norayr-noro/Devboard-RGB-LED-custom_button_I2C_header/Photoss/PCB_screenshot(3d-front).png

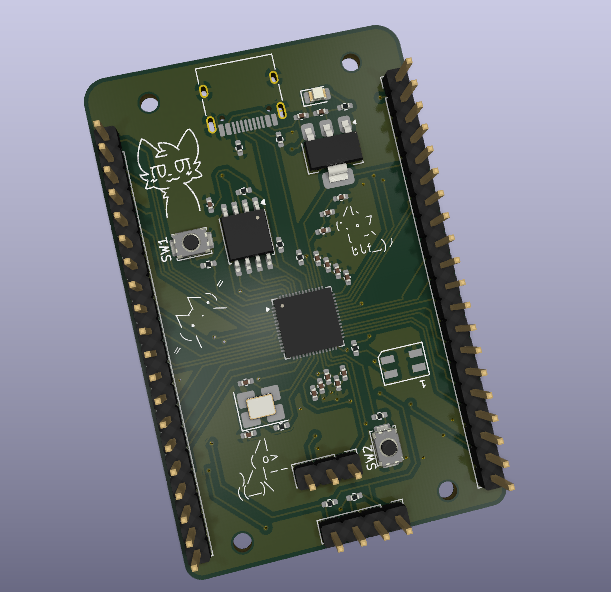
Photoss/PCB_screenshot(3d-front).png
