norayr-noro/Devboard-RGB-LED-custom_button_I2C_header/Photoss/Screenshot 2026-04-28 124610.png

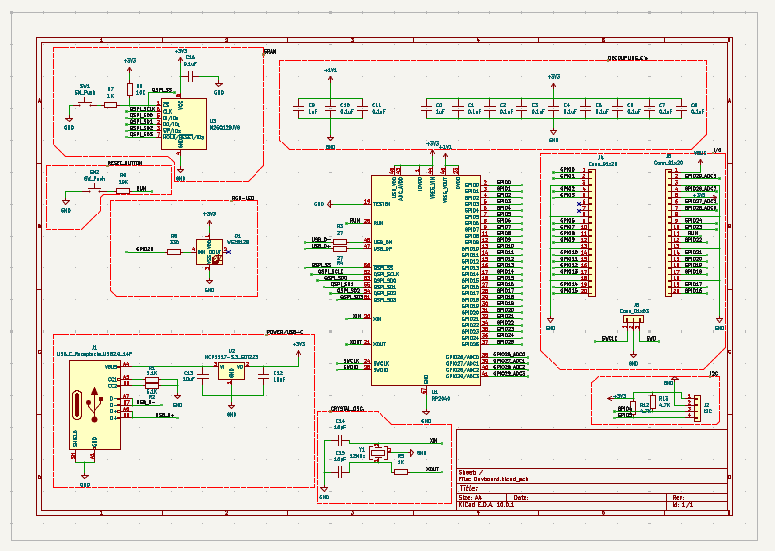
Photoss/Screenshot 2026-04-28 124610.png
